marcvaldez/Search-and-Rescue-Robot/Arduino/RobotEye/camera_index.h

#define index_ov2640_html_gz_len 1290
const uint8_t index_ov2640_html_gz[] = {
0x1f,0x8b,0x08,0x00,0xd0,0x8c,0xd6,0x5e,0x00,0xff,0xad,0x57,0x51,0x6f,0xdb,0x36,0x10,0x7e,0xb6,0x7f,0xc5,0x4d,0x7b,0x88,0x83,0x2e,0xd2,0x92,0x6e,0x5d,0xea,0xda,0x06,0x96,0x34,0x45,0x0b,0xa4,0xed,0x90,0xa4,0x2b,0xf6,0x54,0xd0,0xd2,0x59,0x66,0x2b,0x91,0x06,0x49,0xd9,0xf3,0x86,0xfc,0xf7,0xde,0x91,0xb2,0x64,0x3b,0xf1,0xec,0x15,0xf5,0x83,0x4d,0x93,0xf7,0xdd,0x1d,0x8f,0xf7,0x7d,0x94,0x06,0x3f,0xbc,0x7c,0x7f,0x79,0xf7,0xd7,0x1f,0x57,0x30,0x75,0x65,0x31,0xea,0x0e,0xf8,0x07,0x0a,0xa1,0xf2,0x61,0x84,0x2a,0xe2,0x09,0x14,0xd9,0xa8,0xdb,0x19,0x94,0xe8,0x04,0xa4,0x53,0x61,0x2c,0xba,0x61,0xf4,0xe1,0xee,0xd5,0xc9,0x39,0x2d,0x77,0x06,0x4e,0xba,0x02,0x47,0xb7,0x28,0x4c,0x3a,0x05,0xa1,0x32,0xb8,0x41,0x9b,0x56,0x08,0x37,0x7a,0xac,0xdd,0x20,0x09,0xcb,0x64,0x67,0xdd,0x92,0x07,0x63,0x9d,0x2d,0x61,0x04,0x99,0x9c,0xc3,0xbf,0xdd,0x4e,0x26,0xed,0xac,0x10,0xcb,0x3e,0x4c,0x0a,0xfc,0xfb,0x45,0xb7,0xf3,0xb9,0xb2,0x4e,0x4e,0x96,0x27,0xa9,0x56,0x0e,0x95,0xeb,0x43,0x4a,0xdf,0x68,0x68,0x45,0x14,0x32,0x57,0x27,0xd2,0x61,0x69,0xdb,0xd9,0xfb,0xee,0xb8,0x72,0x4e,0x2b,0x76,0xb5,0x90,0x99,0x9b,0xf6,0xe1,0x37,0x2c,0xc9,0x7a,0x8a,0x32,0x9f,0x12,0x3c,0xfc,0x9b,0x90,0xb7,0x13,0x2b,0xff,0xc1,0x3e,0x9c,0xb5,0x13,0x8b,0xda,0x66,0xac,0x8b,0x8c,0xe6,0x4a,0x61,0x72,0xa9,0xfa,0xf0,0x14,0x4b,0x38,0x8d,0x7f,0x65,0xbb,0xfb,0x6e,0x4c,0x79,0x5e,0xfa,0x60,0x94,0x73,0x1b,0xab,0x49,0x7b,0x5c,0xe8,0xf4,0x0b,0x1b,0xfe,0x68,0x9d,0x41,0x51,0xae,0x25,0xf2,0xec,0x97,0x9f,0x67,0xb4,0x25,0x5a,0x32,0x62,0xb1,0x01,0x52,0x5a,0x61,0x8d,0x11,0xae,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
0x04,0xd3,0x4d,0x3c,0x2b,0xd9,0x21,0xe0,0xa2,0x51,0xbc,0x26,0x32,0x4b,0xd9,0x41,0x71,0x5b,0xcd,0x5b,0x61,0x59,0xe5,0x0f,0x81,0xda,0xe6,0x36,0x58,0x21,0x59,0xb1,0x0f,0x2a,0x56,0xa3,0xec,0xcd,0x4e,0xf9,0x8a,0x38,0x68,0xab,0xed,0x5d,0xb2,0xc2,0x7a,0xc1,0x3f,0x04,0xab,0x1e,0xd6,0x29,0x68,0xfe,0x41,0xe0,0xcd,0x4a,0xdd,0xd3,0x80,0x5f,0x80,0xea,0x07,0x55,0x7a,0x05,0x0a,0xef,0x3e,0xf4,0x2a,0xc4,0x2f,0xb1,0x5f,0x01,0x7c,0xa0,0xb5,0x86,0xd4,0x0e,0x00,0x00
};
